SinisterRj/SafetyPrinter/ArduinoFirmware/Thermistor.ino

//*************************        Thermistor module       *************************
/*
 * Copyright (c) 2021~22 Rodrigo C. C. Silva [https://github.com/SinisterRj/SafetyPrinter]
 *
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
 * 
 * WARNIG: DON'T CHANGE ANYTHING IN THIS FILE! ALL CONFIGURATIONS SHOULD BE DONE IN "Configurations.h".
*/

#define SAMPLES               20          // Number of samples for NTC thermistor. Smaller number will add some noise to signal, greater number will add some delay on sample acquisition.

#define OV(N) int16_t(N)   //((N)*(SAMPLES))
#define COUNT(a) (sizeof(a)/sizeof(*a))

typedef int16_t celsius_t;
typedef struct { int16_t value; celsius_t celsius; } temp_entry_t;

#define ANY_THERMISTOR_IS(n) (SENSOR_1_TEMP_TYPE == n || SENSOR_2_TEMP_TYPE == n || SENSOR_3_TEMP_TYPE == n || SENSOR_4_TEMP_TYPE == n || SENSOR_5_TEMP_TYPE == n || SENSOR_6_TEMP_TYPE == n || SENSOR_7_TEMP_TYPE == n || SENSOR_8_TEMP_TYPE == n )

#if ANY_THERMISTOR_IS(1) // 100k bed thermistor
  #include "tables/thermistor_1.h"
#endif
#if ANY_THERMISTOR_IS(2) // 200k bed thermistor
  #include "tables/thermistor_2.h"
#endif
#if ANY_THERMISTOR_IS(3) // mendel-parts
  #include "tables/thermistor_3.h"
#endif
#if ANY_THERMISTOR_IS(4) // 10k thermistor
  #include "tables/thermistor_4.h"
#endif
#if ANY_THERMISTOR_IS(5) // 100k ParCan thermistor (104GT-2)
  #include "tables/thermistor_5.h"
#endif
#if ANY_THERMISTOR_IS(6) // 100k Epcos thermistor
  #include "tables/thermistor_6.h"
#endif
#if ANY_THERMISTOR_IS(7) // 100k Honeywell 135-104LAG-J01
  #include "tables/thermistor_7.h"
#endif
#if ANY_THERMISTOR_IS(8) // 100k 0603 SMD Vishay NTCS0603E3104FXT (4.7k pullup)
  #include "tables/thermistor_8.h"
#endif
#if ANY_THERMISTOR_IS(9) // 100k GE Sensing AL03006-58.2K-97-G1 (4.7k pullup)
  #include "tables/thermistor_9.h"
#endif
#if ANY_THERMISTOR_IS(10) // 100k RS thermistor 198-961 (4.7k pullup)
  #include "tables/thermistor_10.h"
#endif
#if ANY_THERMISTOR_IS(11) // QU-BD silicone bed QWG-104F-3950 thermistor
  #include "tables/thermistor_11.h"
#endif
#if ANY_THERMISTOR_IS(12) // 100k 0603 SMD Vishay NTCS0603E3104FXT (4.7k pullup) (calibrated for Makibox hot bed)
  #include "tables/thermistor_12.h"
#endif
#if ANY_THERMISTOR_IS(13) // Hisens thermistor B25/50 =3950 +/-1%
  #include "tables/thermistor_13.h"
#endif
#if ANY_THERMISTOR_IS(15) // JGAurora A5 thermistor calibration
  #include "tables/thermistor_15.h"
#endif
#if ANY_THERMISTOR_IS(17) // Dagoma NTC 100k white thermistor
  #include "tables/thermistor_17.h"
#endif
#if ANY_THERMISTOR_IS(18) // ATC Semitec 204GT-2 (4.7k pullup) Dagoma.Fr - MKS_Base_DKU001327
  #include "tables/thermistor_18.h"
#endif
#if ANY_THERMISTOR_IS(20) // PT100 with INA826 amp on Ultimaker v2.0 electronics
  #include "tables/thermistor_20.h"
#endif
#if ANY_THERMISTOR_IS(21) // Pt100 with INA826 amp with 3.3v excitation based on "Pt100 with INA826 amp on Ultimaker v2.0 electronics"
  #include "tables/thermistor_21.h"
#endif
#if ANY_THERMISTOR_IS(22) // Thermistor in a Rostock 301 hot end, calibrated with a multimeter
  #include "tables/thermistor_22.h"
#endif
#if ANY_THERMISTOR_IS(23) // By AluOne #12622. Formerly 22 above. May need calibration/checking.
  #include "tables/thermistor_23.h"
#endif
#if ANY_THERMISTOR_IS(30) // Kis3d Silicone mat 24V 200W/300W with 6mm Precision cast plate (EN AW 5083)
  #include "tables/thermistor_30.h"
#endif
#if ANY_THERMISTOR_IS(51) // 100k EPCOS (WITH 1kohm RESISTOR FOR PULLUP, R9 ON SANGUINOLOLU! NOT FOR 4.7kohm PULLUP! THIS IS NOT NORMAL!)
  #include "tables/thermistor_51.h"
#endif
#if ANY_THERMISTOR_IS(52) // 200k ATC Semitec 204GT-2 (WITH 1kohm RESISTOR FOR PULLUP, R9 ON SANGUINOLOLU! NOT FOR 4.7kohm PULLUP! THIS IS NOT NORMAL!)
  #include "tables/thermistor_52.h"
#endif
#if ANY_THERMISTOR_IS(55) // 100k ATC Semitec 104GT-2 (Used on ParCan) (WITH 1kohm RESISTOR FOR PULLUP, R9 ON SANGUINOLOLU! NOT FOR 4.7kohm PULLUP! THIS IS NOT NORMAL!)
  #include "tables/thermistor_55.h"
#endif
#if ANY_THERMISTOR_IS(60) // Maker's Tool Works Kapton Bed Thermistor
  #include "tables/thermistor_60.h"
#endif
#if ANY_THERMISTOR_IS(61) // beta25 = 3950 K, R25 = 100 kOhm, Pull-up = 4.7 kOhm, "Formbot 350°C Thermistor"
  #include "tables/thermistor_61.h"
#endif
#if ANY_THERMISTOR_IS(66) // DyzeDesign 500°C Thermistor
  #include "tables/thermistor_66.h"
#endif
#if ANY_THERMISTOR_IS(67) // R25 = 500 KOhm, beta25 = 3800 K, 4.7 kOhm pull-up, SliceEngineering 450 °C Thermistor
  #include "tables/thermistor_67.h"
#endif
#if ANY_THERMISTOR_IS(70) // bqh2 stock thermistor
  #include "tables/thermistor_70.h"
#endif
#if ANY_THERMISTOR_IS(71) // 100k Honeywell 135-104LAF-J01
  #include "tables/thermistor_71.h"
#endif
#if ANY_THERMISTOR_IS(75) // Many of the generic silicon heat pads use the MGB18-104F39050L32 Thermistor
  #include "tables/thermistor_75.h"
#endif
#if ANY_THERMISTOR_IS(99) // 100k bed thermistor with a 10K pull-up resistor
  #include "tables/thermistor_99.h"
#endif
#if ANY_THERMISTOR_IS(331) // Like table 1, but with 3V3 as input voltage for MEGA
  #include "tables/thermistor_331.h"
#endif
#if ANY_THERMISTOR_IS(332) // Like table 1, but with 3V3 as input voltage for DUE
  #include "tables/thermistor_332.h"
#endif
#if ANY_THERMISTOR_IS(666) // beta25 = UNK, R25 = 200K, Pull-up = 10 kOhm, "Unidentified 200K NTC thermistor (Einstart S)"
  #include "tables/thermistor_666.h"
#endif
#if ANY_THERMISTOR_IS(998) // User-defined table 1
  #include "tables/thermistor_998.h"
#endif
#if ANY_THERMISTOR_IS(999) // User-defined table 2
  #include "tables/thermistor_999.h"
#endif


#ifdef SENSOR_1_TEMP_TYPE
  #define SENSOR_1_TEMPTABLE TT_NAME(SENSOR_1_TEMP_TYPE)  
  #define SENSOR_1_TEMPTABLE_LEN COUNT(SENSOR_1_TEMPTABLE)
#else
  #define SENSOR_1_TEMPTABLE NULL
  #define SENSOR_1_TEMPTABLE_LEN 0
#endif

#ifdef SENSOR_2_TEMP_TYPE
  #define SENSOR_2_TEMPTABLE TT_NAME(SENSOR_2_TEMP_TYPE) 
  #define SENSOR_2_TEMPTABLE_LEN COUNT(SENSOR_2_TEMPTABLE) 
#else
  #define SENSOR_2_TEMPTABLE NULL
  #define SENSOR_2_TEMPTABLE_LEN 0
#endif

#ifdef SENSOR_3_TEMP_TYPE
  #define SENSOR_3_TEMPTABLE TT_NAME(SENSOR_3_TEMP_TYPE)  
  #define SENSOR_3_TEMPTABLE_LEN COUNT(SENSOR_3_TEMPTABLE)
#else
  #define SENSOR_3_TEMPTABLE NULL
  #define SENSOR_3_TEMPTABLE_LEN 0
#endif

#ifdef SENSOR_4_TEMP_TYPE
  #define SENSOR_4_TEMPTABLE TT_NAME(SENSOR_4_TEMP_TYPE) 
  #define SENSOR_4_TEMPTABLE_LEN COUNT(SENSOR_4_TEMPTABLE) 
#else
  #define SENSOR_4_TEMPTABLE NULL
  #define SENSOR_4_TEMPTABLE_LEN 0
#endif

#ifdef SENSOR_5_TEMP_TYPE
  #define SENSOR_5_TEMPTABLE TT_NAME(SENSOR_5_TEMP_TYPE)  
  #define SENSOR_5_TEMPTABLE_LEN COUNT(SENSOR_5_TEMPTABLE)
#else
  #define SENSOR_5_TEMPTABLE NULL
  #define SENSOR_5_TEMPTABLE_LEN 0
#endif

#ifdef SENSOR_6_TEMP_TYPE
  #define SENSOR_6_TEMPTABLE TT_NAME(SENSOR_6_TEMP_TYPE)
  #define SENSOR_6_TEMPTABLE_LEN COUNT(SENSOR_6_TEMPTABLE)  
#else
  #define SENSOR_6_TEMPTABLE NULL
  #define SENSOR_6_TEMPTABLE_LEN 0
#endif

#ifdef SENSOR_7_TEMP_TYPE
  #define SENSOR_7_TEMPTABLE TT_NAME(SENSOR_7_TEMP_TYPE)
  #define SENSOR_7_TEMPTABLE_LEN COUNT(SENSOR_7_TEMPTABLE)  
#else
  #define SENSOR_7_TEMPTABLE NULL
  #define SENSOR_7_TEMPTABLE_LEN 0
#endif

#ifdef SENSOR_8_TEMP_TYPE
  #define SENSOR_8_TEMPTABLE TT_NAME(SENSOR_8_TEMP_TYPE) 
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
        #endif
        break;
      case 7:
        #ifdef SENSOR_8_TEMP_TYPE
          if (PGM_RD_W(SENSOR_8_TEMPTABLE[i].celsius) < minTemp) {
              minTemp = PGM_RD_W(SENSOR_8_TEMPTABLE[i].celsius);
          }
        #endif
        break; 
    }            
  }
  return minTemp;
}
