SinisterRj/SafetyPrinter/ArduinoFirmware/Serial.ino

//*************************   Serial communication module  *************************
/*
 * Copyright (c) 2021~22 Rodrigo C. C. Silva [https://github.com/SinisterRj/SafetyPrinter]
 *
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
 * 
 * WARNIG: DON'T CHANGE ANYTHING IN THIS FILE! ALL CONFIGURATIONS SHOULD BE DONE IN "Configurations.h".
*/
#ifdef HAS_SERIAL_COMM

#include <util/crc16.h>
#include <string.h>

#define SENSOR_CHAR  "#"
#define SEP_CHAR     ","
#define CRC_CHAR     "$"
#define COMMANDSIZE  9
#define ARGUMENTSIZE 8

#define STARTMARKER '<'
#define ENDMARKER '>'
#define NUMCHARS 38

const char * const BoolToString(bool b)
{
  return b ? "T" : "F";
}

void recvCommandWithStartEndMarkers() {  
  /* Receive commands from PC
  * 
  * This function receive serial ASCII data and splits it into a "command" and up to 4 "arguments",
  * The sintax must be:
  * <COMAND ARGUMENT1 ARGUMENT2 ARGUMENT3 ARGUMENT4> 
  * 
  */

  static bool recvInProgress = false;
  static byte ndx = 0;
  char rc;
  char receivedChars[NUMCHARS+1] = "";
  //String receivedStr;
  char command[COMMANDSIZE] = "";
  char argument1[ARGUMENTSIZE] = "";
  char argument2[ARGUMENTSIZE] = "";
  char argument3[ARGUMENTSIZE] = "";
  char argument4[ARGUMENTSIZE] = "";
  bool newData = false;
 
  SERIAL.flush();
  
  while (SERIAL.available() > 0 && newData == false) {
      delay(3);
      rc = SERIAL.read();
      if (rc != -1) {
        if (recvInProgress == true ) {
            if (rc != ENDMARKER) {
                receivedChars[ndx] = (char)rc;
                ndx++;
                
                if (ndx >= NUMCHARS) {
                    ndx = NUMCHARS - 1;
                }
            }
            else {
                receivedChars[ndx] = '\0'; // terminate the string
                recvInProgress = false;
                ndx = 0;
                newData = true;
            }
        }
        else if (rc == STARTMARKER) {
            recvInProgress = true;
        }
      }
  }
  if (newData == true) { 
    char * strtokIndx; // this is used by strtok() as an index

    //Splits commands and argumments
            
    strtokIndx = strtok(receivedChars," "); 
    strcpy(command, strtokIndx);
  
    strtokIndx = strtok(NULL," ");   
    strcpy(argument1, strtokIndx); 
  
    strtokIndx = strtok(NULL," ");     
    strcpy(argument2, strtokIndx); 
  
    strtokIndx = strtok(NULL," ");   
    strcpy(argument3, strtokIndx); 
  
    strtokIndx = strtok(NULL," ");     
    strcpy(argument4, strtokIndx); 

    //Identifyes each command
    //Add here if you need to add new commands: MAX 8 chars
    SERIAL.print(command);
    if (String(command).equalsIgnoreCase("c1") || String(command).equalsIgnoreCase("reset")) {
      Cmd_c1();
    } else if ((String(command).equalsIgnoreCase("c2")) || (String(command).equalsIgnoreCase("trip"))) {
      Cmd_c2();        
    } else if ((String(command).equalsIgnoreCase("c3")) || (String(command).equalsIgnoreCase("enable"))) {
      Cmd_c3(argument1,argument2);   
    } else if ((String(command).equalsIgnoreCase("c4")) || (String(command).equalsIgnoreCase("setpoint"))) {
      Cmd_c4(argument1,argument2);        
    } else if ((String(command).equalsIgnoreCase("c5")) || (String(command).equalsIgnoreCase("save"))) {
      Cmd_c5();      
    } else if ((String(command).equalsIgnoreCase("c6")) || (String(command).equalsIgnoreCase("turn"))) {
      Cmd_c6(argument1);
    } else if ((String(command).equalsIgnoreCase("c7")) || (String(command).equalsIgnoreCase("timer"))) {
      Cmd_c7(argument1,argument2);
    } else if ((String(command).equalsIgnoreCase("c8")) || (String(command).equalsIgnoreCase("standard"))) {
      Cmd_c8(argument1);      
    } else if ((String(command).equalsIgnoreCase("c9")) || (String(command).equalsIgnoreCase("flash"))) {
      Cmd_c9(argument1);   
    } else if (String(command).equalsIgnoreCase("r1")) {
      Cmd_r1();
    } else if (String(command).equalsIgnoreCase("r2")) {
      Cmd_r2();
    } else if ((String(command).equalsIgnoreCase("r3")) || (String(command).equalsIgnoreCase("info"))) {
      Cmd_r3();
    } else if (String(command).equalsIgnoreCase("r4")) {
      Cmd_r4();
    } else if (String(command).equalsIgnoreCase("r5")) {
      Cmd_r5();
    } else if (String(command).equalsIgnoreCase("r6")) {
      Cmd_r6();
    } else if ((String(command).equalsIgnoreCase("r7")) || (String(command).equalsIgnoreCase("ispowered"))) {
      Cmd_r7();
    } else if (String(command).equalsIgnoreCase("d1")) {
      Cmd_d1(argument1);
    } else {
      ReturnError(0,command);
    }
  }
}

void ReturnError(int type, char text[ARGUMENTSIZE]){
   // Feedbacks wrong serial commands or arguments
   switch (type) {
      case 1:
      case 2:
      case 3:
      case 4:  
         SERIAL.print(F(": Unknown argument "));
         SERIAL.print(type);
         SERIAL.print(F(":"));
         SERIAL.println(text); 
      break;
      default:
          SERIAL.println(F(": Unknown command!"));
      break;
  }
  #ifdef DEBUG
      SERIAL.print (F("ReturnError: Free memory [bytes]= "));  // 2048 bytes from datasheet
      SERIAL.println (freeMemory());
  #endif
  #ifdef HAS_LCD
      includeExtraMsg(0,0,false);
  #endif
}

void Cmd_c1()
{
   // Serial command to Reset trip condition
   if (interlockStatus) {
      if (resetInterlock(false)) {
         if (printerPowered) {     
            SERIAL.println(F(": Resseting interlocks."));      
         } else {
            SERIAL.println(F(": Resseting interlocks but printer is powered OFF by <C6> command."));      
         } 
         #ifdef HAS_LCD
            includeExtraMsg(0,1,false);
         #endif
      } else {
         SERIAL.print(F(": Can't reset now. Wait "));
         SERIAL.print(MINIMUM_INTERLOCK_DELAY);
         SERIAL.println(F("s and try again."));  
      }
   } else {
      SERIAL.println(F(": No interlock to reset."));   
   }
   #ifdef DEBUG
      SERIAL.print (F("Cmd_c1: Free memory [bytes]= "));  // 2048 bytes from datasheet
      SERIAL.println (freeMemory());
   #endif
}

void Cmd_c2()
{
   // Serial command to Trip
   SERIAL.println(F(": External interlock received."));
   interlock(false,0);
   #ifdef DEBUG
      SERIAL.print (F("Cmd_c2: Free memory [bytes]= "));  // 2048 bytes from datasheet
      SERIAL.println (freeMemory());
   #endif
}

void Cmd_c3(char argument1[ARGUMENTSIZE], char argument2[ARGUMENTSIZE])
{
   // Serial command to enable or dissable a sensor
   if (String(argument1).equalsIgnoreCase("all")) {
      if (String(argument2).equalsIgnoreCase("on")) {
         for (uint8_t i =0; i < numOfSensors; i++) { 
            if (!sensors[i].forceDisable) {
               sensors[i].enabled = true;
            } else {
               sensors[i].enabled = false;
            }
         }   
         SERIAL.println(F(": ALL sensors are ENABLED.")); 
         #ifdef HAS_LCD
             includeExtraMsg(255,2,true);
         #endif 
      } else if (String(argument2).equalsIgnoreCase("off")) {
         for (uint8_t i =0; i < numOfSensors; i++) { 
            sensors[i].enabled = false;
            sensors[i].active = false;
         } 
         SERIAL.println(F(": ALL sensors are DISABLED.")); 
         #ifdef HAS_LCD
             includeExtraMsg(255,3,true);
         #endif  
      }       
   } else {
      int i = atoi(argument1);
      if (i >= 0 and i < numOfSensors and String(argument1).length() > 0) {
         if (String(argument2).equalsIgnoreCase("on")) {
            SERIAL.print(F(": "));
            SERIAL.print(sensors[i].label);
            if (!sensors[i].forceDisable) {
               sensors[i].enabled = true;
               SERIAL.println(F(" is ENABLED."));
                  #ifdef HAS_LCD
                     includeExtraMsg(i,2,true);
                  #endif 
            } else {
               sensors[i].enabled = false;
               SERIAL.println(F(" ERROR: cannot be enabled due to configuration problem.")); 
               #ifdef HAS_LCD
                  includeExtraMsg(0,0,false);
               #endif
            }  
         } else if (String(argument2).equalsIgnoreCase("off")) {
            sensors[i].enabled = false;
            sensors[i].active = false;
            SERIAL.print(F(": "));
            SERIAL.print(sensors[i].label);
            SERIAL.println(F(" is DISABLED."));
            #ifdef HAS_LCD
               includeExtraMsg(i,3,true);
            #endif   
         } else {
            ReturnError(2,argument2);
         }       
      } else {
         ReturnError(1,argument1);
      }
   }
   #ifdef DEBUG
      SERIAL.print (F("Cmd_c3: Free memory [bytes]= "));  // 2048 bytes from datasheet
      SERIAL.println (freeMemory());
   #endif
}

void Cmd_c4(char argument1[ARGUMENTSIZE], char argument2[ARGUMENTSIZE])
{
   // Serial command to change set point
   int i = atoi(argument1);
   if (i >= 0 and i < numOfSensors and String(argument1).length() > 0) {
      int newSP = atoi(argument2);
      int oldSP = sensors[i].alarmSP;
      if ((newSP < sensors[i].lowSP) || (newSP > sensors[i].highSP)) {
         // Wrong value.        
         SERIAL.print(F(": Alarm set point for: "));
         SERIAL.print(sensors[i].label);
         SERIAL.print(F(" must be between or equal to: "));
         SERIAL.print(sensors[i].lowSP);
         SERIAL.print(F(" and "));
         SERIAL.print(sensors[i].highSP);
         #ifdef HAS_LCD
            includeExtraMsg(0,0,false);
         #endif
      } else {
         sensors[i].alarmSP = newSP;   
         SERIAL.print(F(": Sensor: "));
         SERIAL.print(sensors[i].label); 
         SERIAL.print(F(" set point changed from: ")); 
         SERIAL.print(oldSP); 
         SERIAL.print(F(" to: ")); 
         SERIAL.print(sensors[i].alarmSP);
         #ifdef HAS_LCD
             includeExtraMsg(i,4,true);
         #endif 
      }   
      SERIAL.println(F("."));     
   } else {
      ReturnError(1,argument1);
   }
   #ifdef DEBUG
      SERIAL.print (F("Cmd_c4: Free memory [bytes]= "));  // 2048 bytes from datasheet
      SERIAL.println (freeMemory());
   #endif
}

void Cmd_c5()
{
   // Update EEPROM sensors status
   byte bytesSaved = 0;
   bytesSaved = writeEEPROMData();
   SERIAL.print(F(": EEPROM updated. "));
   SERIAL.print(bytesSaved);
   SERIAL.print(F(" bytes saved. "));
   SERIAL.print(EEPROM.length() - bytesSaved);
   SERIAL.println(F(" bytes free."));
   #ifdef HAS_LCD
      includeExtraMsg(0,5,false);
   #endif 
   #ifdef DEBUG
      SERIAL.print (F("Cmd_c5: Free memory [bytes]= "));  // 2048 bytes from datasheet
      SERIAL.println (freeMemory());
   #endif   
}

void Cmd_c6(char argument1[ARGUMENTSIZE])
{
   // Serial command to turn ON/OFF 3d Printer (switching the interlock relay output without changing trip status)
   if (String(argument1).equalsIgnoreCase("off")) {
      // Turns off printer
      if (turnOnOff(false)) {
         SERIAL.println(F(": Printer turned OFF.")); 
         #ifdef HAS_LCD
            includeExtraMsg(0,6,false);
         #endif 
      } else {
         SERIAL.println(F(": Can't turn OFF printer.")); 
      }
   } else if (String(argument1).equalsIgnoreCase("on")) {
      // Turns on printer

      if (!interlockStatus) {
         if (turnOnOff(true)) {
            SERIAL.println(F(": Printer turned ON.")); 
            #ifdef HAS_LCD
               includeExtraMsg(0,7,false);
            #endif  
         } else {
            SERIAL.print(F(": Can't turn printer ON now. Wait "));
            SERIAL.print(MINIMUM_INTERLOCK_DELAY);
            SERIAL.println(F("s and try again."));
         }
      } else {
         SERIAL.println(F(": Can't turn printer ON with INTERLOCK status ON."));
      }
   } else {
      ReturnError(1,argument1);
   }
   #ifdef DEBUG
      SERIAL.print (F("Cmd_c6: Free memory [bytes]= "));  // 2048 bytes from datasheet
      SERIAL.println (freeMemory());
   #endif
}

void Cmd_c7(char argument1[ARGUMENTSIZE], char argument2[ARGUMENTSIZE])
{
   // Serial command to change timer
   int i = atoi(argument1);
   if (i >= 0 and i < numOfSensors and String(argument1).length() > 0) {
      unsigned long newTimer = atol(argument2);
      unsigned long oldTimer = sensors[i].timer;
      if ((newTimer < 0) || (newTimer > 4294967295)) {
         // Wrong value.        
         SERIAL.print(F(": Timer for: "));
         SERIAL.print(sensors[i].label);
         SERIAL.println(F(" must be between or equal to: 0 and 4,294,967,295.")); 
         #ifdef HAS_LCD
            includeExtraMsg(0,0,false);
         #endif
      } else {
         sensors[i].timer = newTimer;   
         SERIAL.print(F(": Sensor: "));
         SERIAL.print(sensors[i].label); 
         SERIAL.print(F(" timer changed from: "));
         SERIAL.print(oldTimer);
         SERIAL.print(F("ms to: "));
         SERIAL.print(sensors[i].timer);
         SERIAL.println(F("ms."));
         #ifdef HAS_LCD
            includeExtraMsg(i,8,true);
         #endif  
      }       
   } else {
      ReturnError(1,argument1);
   }
   #ifdef DEBUG
      SERIAL.print (F("Cmd_c7: Free memory [bytes]= "));  // 2048 bytes from datasheet
      SERIAL.println (freeMemory());
   #endif
}

void Cmd_c8(char argument1[ARGUMENTSIZE])
{
   // Serial command to change sensors enabled, alarm set point and timer to standard values
   if (String(argument1).equalsIgnoreCase("all")) {
      for (int i =0; i < numOfSensors; i++) { 
         sensors[i].enabled = defaultSensors[i].enabled;
         sensors[i].alarmSP = defaultSensors[i].alarmSP;
         sensors[i].timer = defaultSensors[i].timer;
      }   
      SERIAL.println(F(": ALL sensors configurations returned to standard values."));
      #ifdef HAS_LCD
         includeExtraMsg(255,9,true);
      #endif  
   } else {
     int i = atoi(argument1);
     if (i >= 0 and i < numOfSensors and String(argument1).length() > 0) {
         sensors[i].enabled = defaultSensors[i].enabled;
         sensors[i].alarmSP = defaultSensors[i].alarmSP;
         sensors[i].timer = defaultSensors[i].timer;
         SERIAL.print(F(": Sensor: "));
         SERIAL.print(sensors[i].label);
         SERIAL.println(F(" configurations returned to standard values.")); 
         #ifdef HAS_LCD
            includeExtraMsg(i,9,true);
         #endif  
     } else {
        ReturnError(1,argument1);
     }
   }
   #ifdef DEBUG
      SERIAL.print (F("Cmd_c8: Free memory [bytes]= "));  // 2048 bytes from datasheet
      SERIAL.println (freeMemory());
   #endif
}

void Cmd_c9(char argument1[ARGUMENTSIZE])
{
    // Resets Arduino
    #ifdef ARDUINO_RESET_PIN
      unsigned long i = atoi(argument1);
      SERIAL.print(F(": Resseting in bootloader mode in "));
      SERIAL.print(i);
      SERIAL.println(F(" miliseconds."));
      
      #ifdef DEBUG
          SERIAL.print (F("Cmd_c5: Free memory [bytes]= "));  // 2048 bytes from datasheet
          SERIAL.println (freeMemory());
      #endif  
      SERIAL.flush();
      delay(i+50);
      digitalWrite(ARDUINO_RESET_PIN, LOW);
    #else
      SERIAL.print(F(": ERROR: ARDUINO_RESET_PIN not defined in configuration.h."));
    #endif
    
}

void Cmd_r1() //530
{
  // Serial command to Return Input Status for Octoprint plugin
  char bfr[20] = "";

  String response = BoolToString(interlockStatus);
  response += SEP_CHAR;

  // Reset inhibit status - included in 0.2.7
  response += BoolToString(inhibitReset);
  response += SEP_CHAR;
  
  // board status
  response += BoolToString(memWrng);
  response += SEP_CHAR;
  memWrng = false;

  response += BoolToString(execWrng);
  response += SEP_CHAR;
  execWrng = false;

  response += BoolToString(tempWrng);
  response += SEP_CHAR;
  tempWrng = false;

  response += BoolToString(voltWrng);
  response += SEP_CHAR;
  voltWrng = false;

  for (int i =0; i < numOfSensors; i++) { 
    response += SENSOR_CHAR;

    memset(bfr, 0, sizeof bfr);
    itoa(i,bfr,10);
    response += bfr;
    response += SEP_CHAR;

    response += BoolToString(sensors[i].enabled);
    response += SEP_CHAR;

    response += BoolToString(sensors[i].active);
    response += SEP_CHAR;

    memset(bfr, 0, sizeof bfr);
    itoa(sensors[i].actualValue,bfr,10);
    response += bfr;
    response += SEP_CHAR;

    memset(bfr, 0, sizeof bfr);
    itoa(sensors[i].alarmSP,bfr,10);
    response += bfr;
    response += SEP_CHAR;
    
    memset(bfr, 0, sizeof bfr);
    itoa(sensors[i].timer,bfr,10);
    response += bfr;
    response += SEP_CHAR;

    response += BoolToString(sensors[i].trigger);
    response += SEP_CHAR;

  }   
  send(response.c_str());  //Sends response with CRC
  #ifdef DEBUG
    SERIAL.print (F("Cmd_r1: Free memory [bytes]= "));  // 2048 bytes from datasheet
    SERIAL.println (freeMemory());
  #endif 
}

void Cmd_r2()
{
   // Serial command to Return Input Labels for Octoprint plugin
   String response = "";
   char bfr[20] = "";

   for (int i =0; i < numOfSensors; i++) { 
      response += SENSOR_CHAR;
      itoa(i,bfr,10);
      response += bfr;
      response += SEP_CHAR;
      response += sensors[i].label;
      response += SEP_CHAR;

      memset(bfr, 0, sizeof bfr);
      itoa(sensors[i].type,bfr,10);
      response += bfr;
      response += SEP_CHAR;

      response += BoolToString(sensors[i].forceDisable);
      response += SEP_CHAR;

      memset(bfr, 0, sizeof bfr);
      itoa(sensors[i].lowSP,bfr,10);
      response += bfr;
      response += SEP_CHAR;
      
      memset(bfr, 0, sizeof bfr);
      itoa(sensors[i].highSP,bfr,10);
      response += bfr;
      response += SEP_CHAR;
   }
   send(response.c_str());  //Sends response with CRC
   #ifdef DEBUG
      SERIAL.print (F("Cmd_r2: Free memory [bytes]= "));  // 2048 bytes from datasheet
      SERIAL.println (freeMemory());
   #endif  
}

void Cmd_r3()
{
  // Serial command to Return Input Status more suitable for humans.
  SERIAL.println(F(": Safety Printer Status"));
  SERIAL.println(F("------------------------------------------------------------------------"));
  SERIAL.print(F("** Interlock Status ** :"));
  if (interlockStatus) SERIAL.println(F(" ********  Shutdown (TRIP) ********")); 
  else SERIAL.println(F(" Normal Operation")); 
  if (inhibitReset) SERIAL.println(F("WARNING: Reset button disabled due to continous operation."));    
  SERIAL.println(F("------------------------------------------------------------------------"));
  SERIAL.println(F("#:| Label ........... | Enab.| Act.| Trig.| Value | S.Point | Timer ... |"));
  for (int i = 0; i < numOfSensors; i++) { 
    SERIAL.print(String(i) + ".|." + sensors[i].label);
    int dots = 18 - strlen(sensors[i].label); //.length();
    for (int j = 0; j< dots ;j++)
    {
        SERIAL.print(F("."));
    }
    SERIAL.print(F("|."));
    if (sensors[i].enabled) {
        SERIAL.print(F("Yes"));
    } else {
        SERIAL.print(F("No."));
    }
    SERIAL.print(F("..|."));
    if (sensors[i].active) {
        SERIAL.print(F("Yes"));
    } else {
        SERIAL.print(F("No."));
    }
    SERIAL.print(F(".|."));
    if (sensors[i].trigger) {
        SERIAL.print(F("Yes."));
    } else {
        SERIAL.print(F("No.."));
    }
    SERIAL.print(".|." + String(sensors[i].actualValue));
    dots = 6-String(sensors[i].actualValue).length();
    for (int j = 0; j< dots;j++)
    {
        SERIAL.print(F("."));
    }
    SERIAL.print("|." + String(sensors[i].alarmSP));
    dots = 8-String(sensors[i].alarmSP).length();
    for (int j = 0; j< dots;j++)
    {
        SERIAL.print(F("."));
    }
    SERIAL.print("|." + String(sensors[i].timer));
    dots = 10-String(sensors[i].timer).length();
    for (int j = 0; j< dots;j++)
    {
        SERIAL.print(F("."));
    }
    SERIAL.println(F("|"));
  }
  SERIAL.println(F("------------------------------------------------------------------------"));
  #ifdef DEBUG
    SERIAL.print (F("Cmd_r3: Free memory [bytes]= "));  // 2048 bytes from datasheet
    SERIAL.println (freeMemory());
  #endif
}

void Cmd_r4()
{
   // Serial command to Return firmware version and release date 
   String response =  VERSION SEP_CHAR RELEASEDATE SEP_CHAR;
   char bfr[20] = "";
  
   itoa(EEPROMVERSION,bfr,10);
   response += bfr;
   response += SEP_CHAR;

   memset(bfr, 0, sizeof bfr);
   itoa(COMMPROTOCOL,bfr,10);
   response += bfr;
   response += SEP_CHAR;

   #if defined(__AVR_ATmega328P__) || defined(__AVR_ATmega168__) //Arduino NANO and UNO
     response += '1';
   #elif defined(__AVR_ATmega32U4__) || defined(__AVR_ATmega16U4__) //Arduino Leonardo and Micro
     response += '2';
   #endif
   response += SEP_CHAR;
   
   send(response.c_str());  //Sends response with CRC
   #ifdef DEBUG
      SERIAL.print (F("Cmd_r4: Free memory [bytes]= "));  // 2048 bytes from datasheet
      SERIAL.println (freeMemory());
   #endif  
}

void Cmd_r5() 
{
   // Serial command to Return Warning Status for Octoprint plugin
   char bfr[20] = "";

   memset(bfr, 0, sizeof bfr);
   itoa(freeMemory(),bfr,10);
   String response = bfr;
   response += SEP_CHAR;

   memset(bfr, 0, sizeof bfr);
   dtostrf(readTemp(),0,2,bfr);
   response += bfr;
   response += SEP_CHAR;

   memset(bfr, 0, sizeof bfr);
   dtostrf(readVcc(),0,2,bfr);
   response += bfr;
   response += SEP_CHAR;
   
   memset(bfr, 0, sizeof bfr);
   ltoa(lTLastMax,bfr,10);
   response += bfr;
   response += SEP_CHAR;

   memset(bfr, 0, sizeof bfr);
   ltoa(lTLastSum/LOOP_TIME_SAMPLES,bfr,10);
   response += bfr;
   response += SEP_CHAR;

   send(response.c_str());
   #ifdef DEBUG
      SERIAL.print (F("Cmd_r5: Free memory [bytes]= "));  // 2048 bytes from datasheet
      SERIAL.println (freeMemory());
   #endif
}

void Cmd_r6() 
{
   // Repeat intro serial message
   SERIAL.println(F(": Safety Printer MCU ver." VERSION ", release date: " RELEASEDATE)); // Boot end msg. Octoprint Plug in looking for this msg in order to indicate that the arduino ir ready to receive commands.

   #ifdef DEBUG
      SERIAL.print (F("Cmd_c5: Free memory [bytes]= "));  // 2048 bytes from datasheet
      SERIAL.println (freeMemory());
   #endif  
}

void Cmd_r7() {
  // Retuns printer status - Integration with PSU Control Plugin
  SERIAL.print (F(": "));
  SERIAL.println (BoolToString(printerPowered));
}

void Cmd_d1(char argument1[ARGUMENTSIZE]) 
{
   // Raises warnings for debug
   int i = atoi(argument1);

   if (i == 1) {
      memWrng = true;
   } else if (i == 2) {
      execWrng = true;
   } else if (i == 3) {
      tempWrng = true;
   } else if (i == 4) {
      voltWrng = true;
   } else {
      ReturnError(1,argument1);
      return;
   }
   SERIAL.println(": Debug command OK!");
   #ifdef DEBUG
      SERIAL.print (F("Cmd_d1: Free memory [bytes]= "));  // 2048 bytes from datasheet
      SERIAL.println (freeMemory());
   #endif
}
 
uint16_t calcCRC(const char* str)
{
  uint16_t crc=0; // starting value as you like, must be the same before each calculation
  for (unsigned int i=0;i<strlen(str);i++) // for each character in the string
  {
    crc= _crc16_update (crc, str[i]); // update the crc value
  }
  return crc;
}

void send(const char* payload) {
   SERIAL.print(":" CRC_CHAR); 
   SERIAL.print(calcCRC(payload));
   SERIAL.print(CRC_CHAR);
   SERIAL.println(payload);
}



#endif
//***************************************************************************************
