SinisterRj/SafetyPrinter/ArduinoFirmware/Verify_Config.ino

//*************************   Configuration.h verification module  *************************
/*
 * Copyright (c) 2021~22 Rodrigo C. C. Silva [https://github.com/SinisterRj/SafetyPrinter]
 *
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
 * 
 * WARNIG: DON'T CHANGE ANYTHING IN THIS FILE! ALL CONFIGURATIONS SHOULD BE DONE IN "Configurations.h".
*/

#define MIN_PIN           1
#define MAX_PIN           21
#define MAX_PIN_DIGITAL   13

#define A0                14
#define A1                15
#define A2                16
#define A3                17
#define A4                18
#define A5                19
#define A6                20
#define A7                21

// check pin assignment

#ifdef InterlockRelayPin
  #if InterlockRelayPin < MIN_PIN || InterlockRelayPin > MAX_PIN
    #error "Wrong InterlockRelay PIN definition. Check your Configuration.h file."
  #endif
#endif

#ifdef ResetButtonPin
  #if ResetButtonPin < MIN_PIN || ResetButtonPin > MAX_PIN
    #error "Wrong ResetButton PIN definition. Check your Configuration.h file."
  #endif
#endif

#ifdef AlarmLedPin
  #if AlarmLedPin < MIN_PIN || AlarmLedPin > MAX_PIN
    #error "Wrong AlarmLed PIN definition. Check your Configuration.h file."
  #endif
#endif

#ifdef TripLedPin
  #if TripLedPin < MIN_PIN || TripLedPin > MAX_PIN
    #error "Wrong TripLed PIN definition. Check your Configuration.h file."
  #endif 
#endif

#ifdef LCD_SDA_PIN
  #if LCD_SDA_PIN < MIN_PIN || LCD_SDA_PIN > MAX_PIN
    #error "Wrong LCD_SDA PIN definition. Check your Configuration.h file."
  #endif
#endif

#ifdef LCD_SCL_PIN
  #if LCD_SCL_PIN < MIN_PIN || LCD_SCL_PIN > MAX_PIN
    #error "Wrong LCD_SCL PIN definition. Check your Configuration.h file."
  #endif
#endif

#ifdef Sensor1Pin
  #if Sensor1Pin < MIN_PIN || Sensor1Pin > MAX_PIN
    #error "Wrong Sensor 1 PIN definition. Check your Configuration.h file."
  #endif
#endif
#ifdef Sensor1AuxPin
  #if Sensor1AuxPin < MIN_PIN || Sensor1AuxPin > MAX_PIN_DIGITAL
    #error "Wrong Sensor 1 Aux PIN definition. Check your Configuration.h file."
  #endif
#endif
#ifdef Sensor1Type 
  #if Sensor1Type != DigitalSensor && Sensor1Type != NTCSensor
    #error "Wrong Sensor 1 TYPE definition. Check your Configuration.h file."
  #endif
  #if Sensor1Type == DigitalSensor && Sensor1AlarmSP != HIGH && Sensor1AlarmSP != LOW
    #error  "Wrong Sensor 1 ALARM SET POINT definition. Check your Configuration.h file. Sensor disabled."
  #endif
#endif

#ifdef Sensor2Pin
  #if Sensor2Pin < MIN_PIN || Sensor2Pin > MAX_PIN
    #error "Wrong Sensor 2 PIN definition. Check your Configuration.h file."
  #endif
#endif
#ifdef Sensor2AuxPin
  #if Sensor2AuxPin < MIN_PIN || Sensor2AuxPin > MAX_PIN_DIGITAL
    #error "Wrong Sensor 2 Aux PIN definition. Check your Configuration.h file."
  #endif
#endif
#ifdef Sensor2Type 
  #if Sensor2Type != DigitalSensor && Sensor2Type != NTCSensor
    #error "Wrong Sensor 2 TYPE definition. Check your Configuration.h file."
  #endif
  #if Sensor2Type == DigitalSensor && Sensor2AlarmSP != HIGH && Sensor2AlarmSP != LOW
    #error  "Wrong Sensor 2 ALARM SET POINT definition. Check your Configuration.h file. Sensor disabled."
  #endif
#endif

#ifdef Sensor3Pin
  #if Sensor3Pin < MIN_PIN || Sensor3Pin > MAX_PIN
    #error "Wrong Sensor 3 PIN definition. Check your Configuration.h file."
  #endif
#endif
#ifdef Sensor3AuxPin
  #if Sensor3AuxPin < MIN_PIN || Sensor3AuxPin > MAX_PIN_DIGITAL
    #error "Wrong Sensor 3 Aux PIN definition. Check your Configuration.h file."
  #endif
#endif
#ifdef Sensor3Type 
  #if Sensor3Type != DigitalSensor && Sensor3Type != NTCSensor
    #error "Wrong Sensor 3 TYPE definition. Check your Configuration.h file."
  #endif
  #if Sensor3Type == DigitalSensor && Sensor3AlarmSP != HIGH && Sensor3AlarmSP != LOW
    #error  "Wrong Sensor 3 ALARM SET POINT definition. Check your Configuration.h file. Sensor disabled."
  #endif
#endif

#ifdef Sensor4Pin
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
    #error "Wrong Sensor 8 TYPE definition. Check your Configuration.h file."
  #endif
  #if Sensor8Type == DigitalSensor && Sensor8AlarmSP != HIGH && Sensor8AlarmSP != LOW
    #error  "Wrong Sensor 8 ALARM SET POINT definition. Check your Configuration.h file. Sensor disabled."
  #endif
#endif
